thienhaiblue/ampm_personal_tracker/firmware/source/src/cpu/start.c

/*
 * File:	start.c
 * Purpose:	Kinetis L Family start up routines. 
 *
 * Notes:		
 */

#include "start.h"
#include "common.h"
#include "sysinit.h"
#include "rcm.h"
#include "dbg_cfg_app.h"
#define START_Info(...)		//DbgCfgPrintf(__VA_ARGS__)

/********************************************************************/
/*!
 * \brief   Kinetis L Family Start
 * \return  None
 *
 * This function calls all of the necessary startup routines and then 
 * branches to the main process.
 */
void start(void)
{            
		/* Disable the watchdog timer */
    SIM_COPC = 0x00;
    
#ifndef CMSIS    // If conforming to CMSIS, we do not need to perform this code


	/* Copy any vector or data sections that need to be in RAM */
	common_startup();
#endif

	/* Perform clock initialization, default UART initialization,
     * initializes clock out function, and enables the abort button
     */
	sysinit();
   uart_init(UART1_BASE_PTR,periph_clk_khz,115200);     
  //START_Info("\n\r\n\r");
	
	/* Determine the last cause(s) of reset */
	outSRS();	
	
	/* Determine specific Kinetis L Family device and revision */
	//cpu_identify();
	
#ifndef CMSIS    // If conforming to CMSIS, we do not need to perform this code
	/* Jump to main process */
	main();

	/* No actions to perform after this so wait forever */
	while(1);
#endif 
}
/********************************************************************/
/*!
 * \brief   Kinetis L Family Identify
 * \return  None
 *
 * This is primarly a reporting function that displays information
 * about the specific CPU to the default terminal including:
 * - Kinetis family
 * - package
 * - die revision
 * - P-flash size
 * - Ram size
 */
void cpu_identify (void)
{
  uint16 temp;
    /* Determine the Kinetis family */
    switch((SIM_SDID & SIM_SDID_FAMID(0x7))>>SIM_SDID_FAMID_SHIFT) 
    {  
    	case 0x0:
    		START_Info("\n\rKL0");
    		break;
    	case 0x1:
    		START_Info("\n\rKL1");
    		break;
    	case 0x2:
    		START_Info("\n\rKL2");
    		break;
    	case 0x3:
    		START_Info("\n\rKL3");
    		break;
    	case 0x4:
    		START_Info("\n\rKL4");
    		break;
	default:
		START_Info("\n\rUnrecognized Kinetis family device.\n\r");  
		break;  	
    }
    
    /* Determine Sub-Family ID */
    switch((SIM_SDID & SIM_SDID_SUBFAMID(0x7))>>SIM_SDID_SUBFAMID_SHIFT) 
    {  
    	case 0x4:
    		START_Info("4");
    		break;
    	case 0x5:
    		START_Info("5");
    		break;
	default:
		START_Info("\n\rUnrecognized Kinetis sub-family device.\n\r");  
		break;  	
    }
    
    /* Determine the package size */
    switch((SIM_SDID & SIM_SDID_PINID(0xF))>>SIM_SDID_PINID_SHIFT) 
    {  
    	case 0x0:
    		START_Info("16pin       ");
    		break;
    	case 0x1:
    		START_Info("24pin       ");
    		break;
    	case 0x2:
    		START_Info("32pin      ");
    		break;
    	case 0x4:
    		START_Info("48pin      ");
    		break;
    	case 0x5:
    		START_Info("64pin      ");
        case 0x6:
    		START_Info("80pin      ");
        case 0x8:
    		START_Info("100pin      ");        
    		break;
	default:
		START_Info("\n\rUnrecognized Kinetis package code.      ");  
		break;  	
    }
    
    /* Determine Attribute ID */
    switch((SIM_SDID & SIM_SDID_SERIESID(0x7))>>SIM_SDID_SERIESID_SHIFT) 
    {  
    	case 0x1:
    		START_Info("\n\rLow Power Line with Cortex M0+\n\r\n\r");
    		break;
	default:
		START_Info("\n\rUnrecognized Kinetis family attribute.\n\r");  
		break;  	
    }
    
    /* Determine the System SRAM Size */
    switch((SIM_SDID & SIM_SDID_SRAMSIZE(0x7))>>SIM_SDID_SRAMSIZE_SHIFT) 
    {  
    	case 0x0:
          START_Info("SRAM Size: 0.5 KB\n\r");
    		break;
        case 0x1:
          START_Info("SRAM Size:  1 KB\n\r");
          break;
        case 0x2:
          START_Info("SRAM Size:  2 KB\n\r");
          break;
        case 0x3:
          START_Info("SRAM Size:  4 KB\n\r");
          break;
        case 0x4:
          START_Info("SRAM Size:  8 KB\n\r");
          break;
        case 0x5:
          START_Info("SRAM Size:  16 KB\n\r");
          break;
        case 0x6:
          START_Info("SRAM Size:  32 KB\n\r");
          break;
        case 0x7:
          START_Info("SRAM Size:  64 KB\n\r");
          break;
	default:
		START_Info("\n\rUnrecognized SRAM Size.\n\r");  
		break;  	
    }                

    /* Determine the revision ID */
    temp = ((SIM_SDID_REVID(0xF))>>SIM_SDID_REVID_SHIFT);
    START_Info("Silicon rev %d\n\r ", temp);
    
    /* Determine the flash revision */
    //flash_identify();    
    
    /* Determine the P-flash size */
  switch((SIM_FCFG1 & SIM_FCFG1_PFSIZE(0xF))>>SIM_FCFG1_PFSIZE_SHIFT)
    {
  	case 0x0:
    		START_Info("Flash size:  8 KB program flash, 0.25 KB protection region");
    		break;
    	case 0x1:
    		START_Info("Flash size:  16 KB program flash, 0.5 KB protection region	");
    		break;
        case 0x3:
    		START_Info("Flash size:  32 KB program flash, 1 KB protection region	");
    		break;
    	case 0x5:
    		START_Info("Flash size:  64 KB program flash, 2 KB protection region	");
    		break;
        case 0x7:
    		START_Info("Flash size:  128 KB program flash, 4 KB protection region	");
    		break;
        case 0x9:
    		START_Info("Flash size:  256 KB program flash, 4 KB protection region	");
    		break;
        case 0xF:
    		START_Info("Flash size:  128 KB program flash, 4 KB protection region	");
    		break;
	default:
		START_Info("ERR!! Undefined flash size\n\r");  
		break;  	  		
    }
}
/********************************************************************/
/*!
 * \brief   flash Identify
 * \return  None
 *
 * This is primarly a reporting function that displays information
 * about the specific flash parameters and flash version ID for 
 * the current device. These parameters are obtained using a special
 * flash command call "read resource." The first four bytes returned
 * are the flash parameter revision, and the second four bytes are
 * the flash version ID.
 */
void flash_identify (void)
{
    /* Get the flash parameter version */

    /* Write the flash FCCOB registers with the values for a read resource command */
    FTFA_FCCOB0 = 0x03;
    FTFA_FCCOB1 = 0x00;
    FTFA_FCCOB2 = 0x00;
    FTFA_FCCOB3 = 0x00;
    FTFA_FCCOB8 = 0x01;

    /* All required FCCOBx registers are written, so launch the command */
    FTFA_FSTAT = FTFA_FSTAT_CCIF_MASK;

    /* Wait for the command to complete */
    while(!(FTFA_FSTAT & FTFA_FSTAT_CCIF_MASK));
    
    START_Info("Flash parameter version %d ",FTFA_FCCOB4);
    START_Info(" %d ",FTFA_FCCOB5);
    START_Info(" %d ",FTFA_FCCOB6);
    START_Info(" %d\n\r",FTFA_FCCOB7);

    /* Get the flash version ID */   

    /* Write the flash FCCOB registers with the values for a read resource command */
    FTFA_FCCOB0 = 0x03;
    FTFA_FCCOB1 = 0x00;
    FTFA_FCCOB2 = 0x00;
    FTFA_FCCOB3 = 0x04;
    FTFA_FCCOB8 = 0x01;

    /* All required FCCOBx registers are written, so launch the command */
    FTFA_FSTAT = FTFA_FSTAT_CCIF_MASK;

    /* Wait for the command to complete */
    while(!(FTFA_FSTAT & FTFA_FSTAT_CCIF_MASK));

    START_Info("Flash version ID %d ",FTFA_FCCOB4);  
    START_Info(" %d",FTFA_FCCOB5);  
    START_Info(" %d ",FTFA_FCCOB6);  
    START_Info("%d\n\r",FTFA_FCCOB7);  
}
/********************************************************************/
