thienhaiblue/ampm_personal_tracker/firmware/source/src/cpu/sysinit.c

/*
 * File:        sysinit.c
 * Purpose:     Kinetis L Family Configuration
 *              Initializes processor to a default state
 *
 * Notes:
 *
 *
 */

#include "common.h"
#include "sysinit.h"

/********************************************************************/

/* Actual system clock frequency */
int mcg_clk_hz;
int mcg_clk_khz;
int core_clk_khz;
int periph_clk_khz;
int pll_clk_khz;
int uart0_clk_khz;



/********************************************************************/
void sysinit (void)
{
        /* Enable all of the port clocks. These have to be enabled to configure
         * pin muxing options, so most code will need all of these on anyway.
         */
        SIM_SCGC5 |= (SIM_SCGC5_PORTA_MASK
                      | SIM_SCGC5_PORTB_MASK
                      | SIM_SCGC5_PORTC_MASK
                      | SIM_SCGC5_PORTD_MASK
                      | SIM_SCGC5_PORTE_MASK );
        
        // releases hold with ACKISO:  Only has an effect if recovering from VLLS1, VLLS2, or VLLS3
        // if ACKISO is set you must clear ackiso before calling pll_init 
        //    or pll init hangs waiting for OSC to initialize
        // if osc enabled in low power modes - enable it first before ack
        // if I/O needs to be maintained without glitches enable outputs and modules first before ack.
        if (PMC_REGSC &  PMC_REGSC_ACKISO_MASK)
        PMC_REGSC |= PMC_REGSC_ACKISO_MASK;
        
        clk_out_init();

#if defined(NO_PLL_INIT)
        
        mcg_clk_hz = 21000000; //FEI mode
        
        SIM_SOPT2 &= ~SIM_SOPT2_PLLFLLSEL_MASK; // clear PLLFLLSEL to select the FLL for this clock source
        
        uart0_clk_khz = (mcg_clk_hz / 1000); // the uart0 clock frequency will equal the FLL frequency
       
#else 
       /* Ramp up the system clock */
       /* Set the system dividers */
       /* NOTE: The PLL init will not configure the system clock dividers,
        * so they must be configured appropriately before calling the PLL
        * init function to ensure that clocks remain in valid ranges.
        */  
 
          
#if 0
   
           /* Configuration for PLL freq = 48MHz */
        SIM_CLKDIV1 = ( 0
                        | SIM_CLKDIV1_OUTDIV1(0)
                        | SIM_CLKDIV1_OUTDIV4(1) );
   
#else        
        

           /* Configuration for PLL freq = 96MHz */
        SIM_CLKDIV1 = ( 0
                        | SIM_CLKDIV1_OUTDIV1(1)
                        | SIM_CLKDIV1_OUTDIV4(1) );
        
#endif
        
        
#ifndef CMSIS        
       /* Initialize PLL */
       /* PLL will be the source for MCG CLKOUT so the core, system, and flash clocks are derived from it */ 
       mcg_clk_hz = pll_init(CLK0_FREQ_HZ,  /* CLKIN0 frequency */
                             LOW_POWER,     /* Set the oscillator for low power mode */
                             CLK0_TYPE,     /* Crystal or canned oscillator clock input */
                             PLL0_PRDIV,    /* PLL predivider value */
                             PLL0_VDIV,     /* PLL multiplier */
                             MCGOUT);       /* Use the output from this PLL as the MCGOUT */

       /* Check the value returned from pll_init() to make sure there wasn't an error */
       if (mcg_clk_hz < 0x100)
         while(1);
			 
			 SIM_SOPT2 |= SIM_SOPT2_PLLFLLSEL_MASK; // set PLLFLLSEL to select the PLL for this clock source
       
       uart0_clk_khz = ((mcg_clk_hz / 2) / 1000); // UART0 clock frequency will equal half the PLL frequency
#else
       mcg_clk_hz = (SystemCoreClock / (((SIM_CLKDIV1 & SIM_CLKDIV1_OUTDIV1_MASK) >> SIM_CLKDIV1_OUTDIV1_SHIFT) + 1));
			 
			 SIM_SOPT2 |= SIM_SOPT2_PLLFLLSEL_MASK; // set PLLFLLSEL to select the PLL for this clock source
       
       uart0_clk_khz = ((SystemCoreClock / 2) / 1000); // UART0 clock frequency will equal half the PLL frequency
#endif
       
			 
#endif      

	/*
         * Use the value obtained from the pll_init function to define variables
	 * for the core clock in kHz and also the peripheral clock. These
	 * variables can be used by other functions that need awareness of the
	 * system frequency.
	 */
        mcg_clk_khz = mcg_clk_hz / 1000;
				core_clk_khz = mcg_clk_khz;
        periph_clk_khz = core_clk_khz / (((SIM_CLKDIV1 & SIM_CLKDIV1_OUTDIV4_MASK) >> 16)+ 1);
        
        /* Enable pin interrupt for the abort button - PTA4 */
        /* This pin could also be used as the NMI interrupt, but since the NMI
         * is level sensitive each button press will cause multiple interrupts.
         * Using the GPIO interrupt instead means we can configure for an edge
         * sensitive interrupt instead = one interrupt per button press.
         */
//        enable_abort_button();
        
#ifdef USE_UART_DEBUG
  	/* UART0 and UART1 are clocked from the core clock, but all other UARTs are
         * clocked from the peripheral clock. So we have to determine which clock
         * to send to the UART_init function.
         */
        if (TERM_PORT_NUM == 0)
            uart0_init (UART0_BASE_PTR, uart0_clk_khz, TERMINAL_BAUD);
        else if (TERM_PORT_NUM == 1)
						uart_init (UART1_BASE_PTR, periph_clk_khz, TERMINAL_BAUD);
        else if (TERM_PORT_NUM == 2)
            uart_init (UART2_BASE_PTR, periph_clk_khz, TERMINAL_BAUD);
        else
          while(1);
#endif 
				
}
/********************************************************************/
void enable_abort_button(void)
{
    /* Configure the PTA4 pin for its GPIO function */
    PORTA_PCR4 = PORT_PCR_MUX(0x1); // GPIO is alt1 function for this pin
    
    /* Configure the PTA4 pin for rising edge interrupts */
    PORTA_PCR4 |= PORT_PCR_IRQC(0x9); 
    
    /* Enable the associated IRQ in the NVIC */
    enable_irq(30);      
}
/********************************************************************/

/********************************************************************/
void clk_out_init(void)
{

          /* Enable the CLKOUT function on PTC3 (alt5 function) */
	  PORTC_PCR3 = ( PORT_PCR_MUX(0x5));
        
          /* Select the CLKOUT in the SMI_SOPT2 mux to be bus clk*/
          SIM_SOPT2 |= SIM_SOPT2_CLKOUTSEL(2);
        
}
