thienhaiblue/ampm_personal_tracker/firmware/source/src/projects/project_main/sys_rtc.c

/**
* \file
*         rtc driver
* \author
*         Nguyen Van Hai <blue@ambo.com.vn>
*/
#include "rtc.h"
#include "tick.h"
#include "stm32f10x_iwdg.h"
#include "sys_time.h"

#define CRL_CNF_Set      ((uint16_t)0x0010)      /* Configuration Flag Enable Mask */
#define CRL_CNF_Reset    ((uint16_t)0xFFEF)      /* Configuration Flag Disable Mask */
#define RTC_LSB_Mask     ((uint32_t)0x0000FFFF)  /* RTC LSB Mask */
#define PRLH_MSB_Mask    ((uint32_t)0x000F0000)  /* RTC Prescaler MSB Mask */


#define RTC_FLAG_RTOFF       ((uint16_t)0x0020)  /* RTC Operation OFF flag */
#define RTC_FLAG_RSF         ((uint16_t)0x0008)  /* Registers Synchronized flag */
#define RTC_FLAG_OW          ((uint16_t)0x0004)  /* Overflow flag */
#define RTC_FLAG_ALR         ((uint16_t)0x0002)  /* Alarm flag */
#define RTC_FLAG_SEC         ((uint16_t)0x0001)  /* Second flag */

#define MAIN_LOOP_TIME_MAX 120 //120sec
#define TIMER0_LOOP_TIME_MAX 60 //60sec
#define TIMER1_LOOP_TIME_MAX 60 //60sec




uint32_t timepowerOffDelay = 0,sec = 0;

volatile uint8_t rtcTimeSecFlagUpdate = 0;
volatile uint32_t rtcTimeSec = 0;
extern uint32_t gpsTimeSec;
extern uint32_t gsmTimeSec;
extern uint32_t rpSampleCount;
extern uint32_t serverSendDataFlag;
extern SYS_STATUS systemStatus;
extern uint32_t batteryPercent;
uint32_t rtcCnt = 0;
uint32_t rtcSecCnt = 0;
uint32_t timeoutSleep = 0;
uint32_t timeoutSleepStatus = MOVING_MODE;
uint32_t batteryWarningCnt = 0;
uint32_t powerWarningCnt = 0;
uint32_t securityOkFlag = 0;
uint32_t autoSecurityCnt = 0;
uint8_t flagAccountCheck = 0;



uint32_t watchdogEnable[WATCHDOG_NUM] = {0};
volatile uint32_t watchdogCnt[WATCHDOG_NUM] = {0};
volatile uint32_t watchdogFeed[WATCHDOG_NUM] = {0};
const uint32_t watchdogCntValueMax[WATCHDOG_NUM] = {MAIN_LOOP_TIME_MAX,TIMER0_LOOP_TIME_MAX,TIMER1_LOOP_TIME_MAX};

extern void MODEM_AgpsProcess(void);
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
